kartoffelfighter/temperatureLogger/wifiSens/Schematic/file5A52C998.sch

## KiCad design wifiSens/Schematic/file5A52C998.sch (2018-06-29)

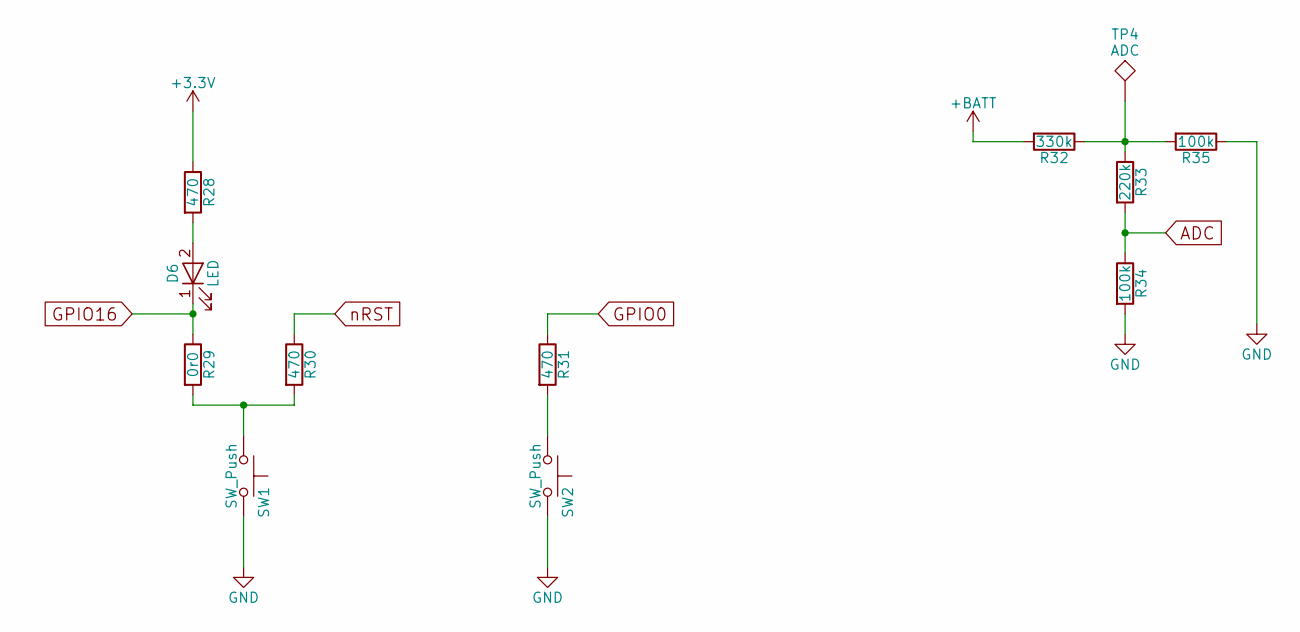
[picture p4: schematic file5A52C998.sch]

Parts:
D6: LED; LED_0805_HandSoldering
R28, R30, R31: 470; R_0603
R29: 0r0; R_0603
R32: 330k; R_0603
R33: 220k; R_0603
R34, R35: 100k; R_0603
SW1, SW2: SW_Push; SW_MEC_5GSH9
TP4: ADC; Pin_Header_Straight_1x01_Pitch1.00mm

Connections:
+3.3V: R28.1
+BATT: R32.2
ADC: R33.2, R34.1
GND: R34.2, R35.1, SW1.2, SW2.2
GPIO0: R31.1
GPIO16: D6.1 (K), R29.1
unnamed: D6.2 (A), R28.2
unnamed: R29.2, R30.2, SW1.1
unnamed: R31.2, SW2.1
unnamed: R32.1, R33.1, R35.2, TP4.1
nRST: R30.1
