kartoffelfighter/temperatureLogger/wifiSens/Schematic/file5A520BA4.sch

## KiCad design wifiSens/Schematic/file5A520BA4.sch (2018-06-29)

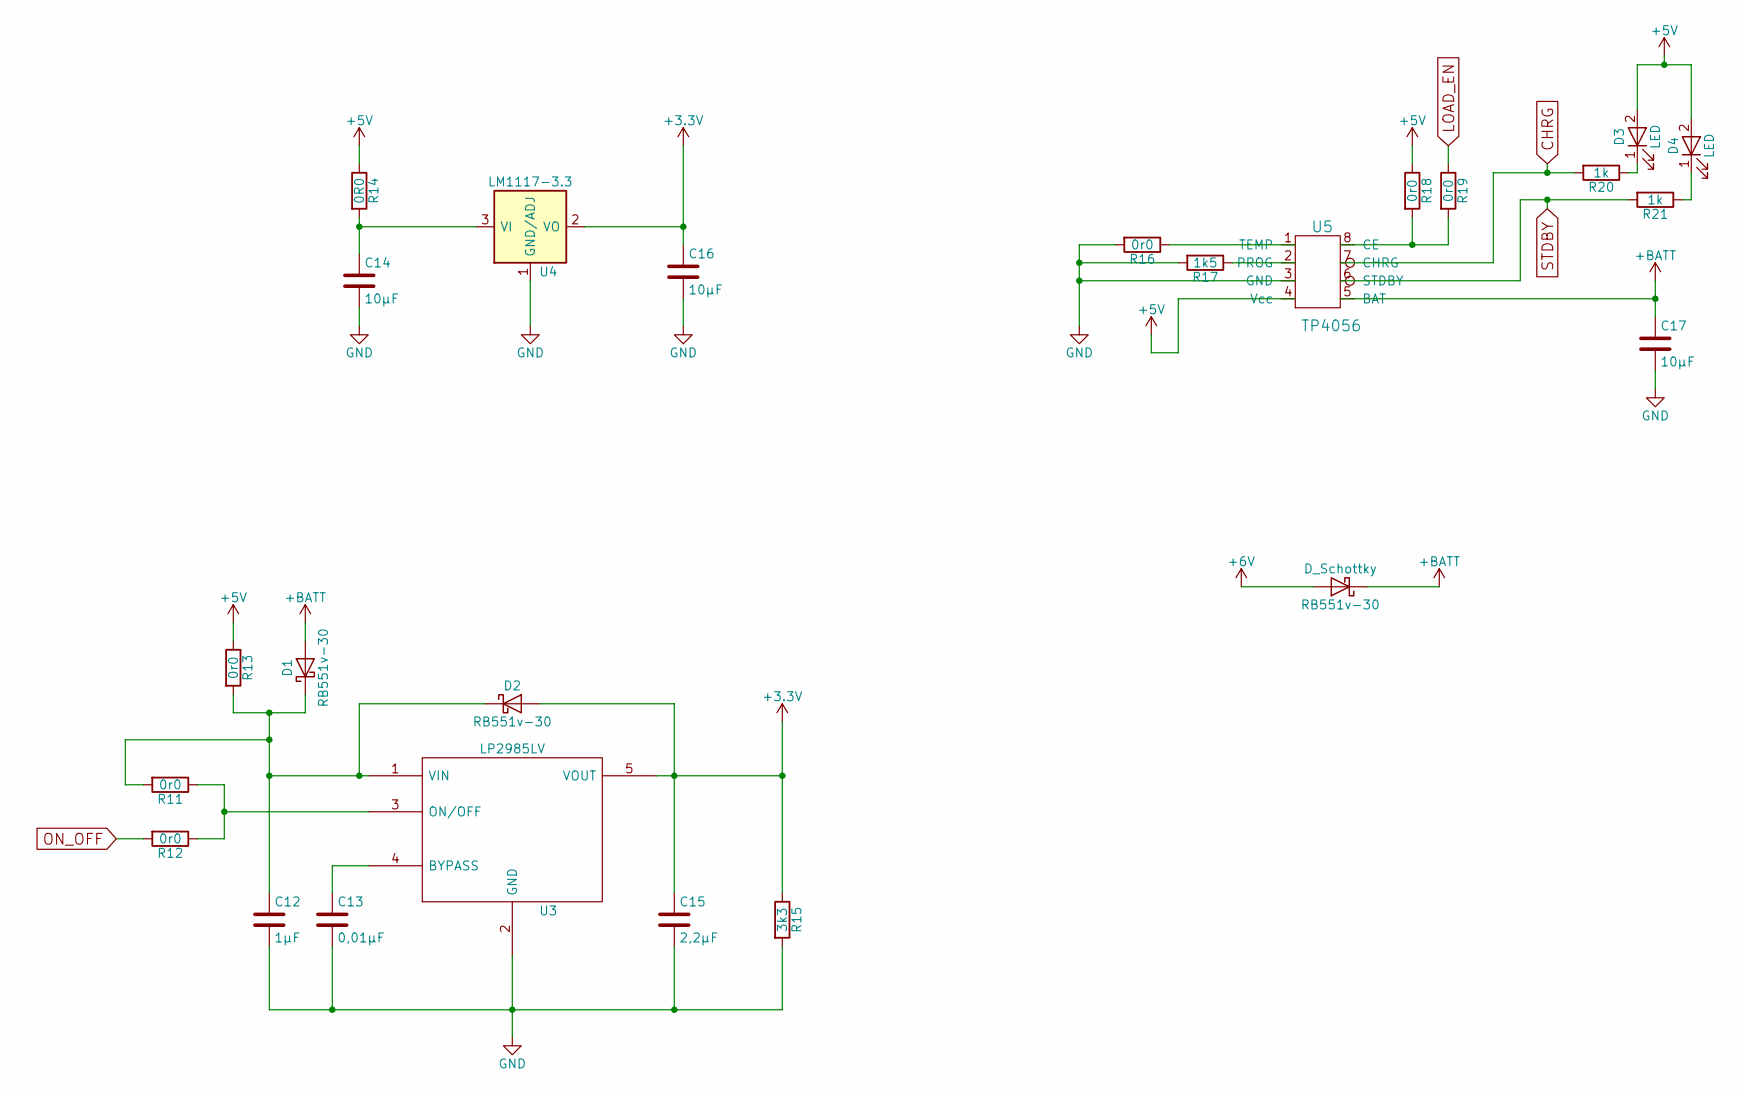
[picture p5: schematic file5A520BA4.sch]

Parts:
C12: 1µF; C_0603_HandSoldering
C13: 0,01µF; C_0603_HandSoldering
C14, C16, C17: 10µF; C_0603_HandSoldering
C15: 2,2µF; C_0603_HandSoldering
D1, D2: RB551v-30; D_SOD-323
D3, D4: LED; LED_0805_HandSoldering
R11, R12, R13, R16, R18, R19: 0r0; R_0603
R14: 0R0; R_0603
R15: 3k3; R_0603
R17: 1k5; R_0603
R20, R21: 1k; R_0603
RB551v-30: D_Schottky; D_SOD-323
U3: LP2985LV; SOT-23-5_HandSoldering
U4: LM1117-3.3; SOT-223
U5: TP4056; SuperSOT-8

Connections:
+3.3V: C15.1, C16.1, D2.2 (A), R15.1, U3.5 (VOUT), U4.2 (VO), U4.4 (VO)
+5V: D3.2 (A), D4.2 (A), R13.1, R14.1, R18.1, U5.4 (Vcc)
+6V: RB551v-30.2 (A)
+BATT: C17.1, D1.2 (A), RB551v-30.1 (K), U5.5 (BAT)
CHRG: R20.2, U5.7 (CHRG)
GND: C12.2, C13.2, C14.2, C15.2, C16.2, C17.2, R15.2, R16.2, R17.2, U3.2 (GND), U4.1 (GND/ADJ), U5.3 (GND)
LOAD_EN: R19.1
unnamed: C12.1, D1.1 (K), D2.1 (K), R11.2, R13.2, U3.1 (VIN)
unnamed: C13.1, U3.4 (BYPASS)
unnamed: C14.1, R14.2, U4.3 (VI)
unnamed: D3.1 (K), R20.1
unnamed: D4.1 (K), R21.1
unnamed: R11.1, R12.1, U3.3 (ON/OFF)
unnamed: R16.1, U5.1 (TEMP)
unnamed: R17.1, U5.2 (PROG)
unnamed: R18.2, R19.2, U5.8 (CE)
ON_OFF: R12.2
STDBY: R21.2, U5.6 (STDBY)
