kartoffelfighter/temperatureLogger/wifiSens/Schematic/file5A520BEC.sch

## KiCad design wifiSens/Schematic/file5A520BEC.sch (2018-06-29)

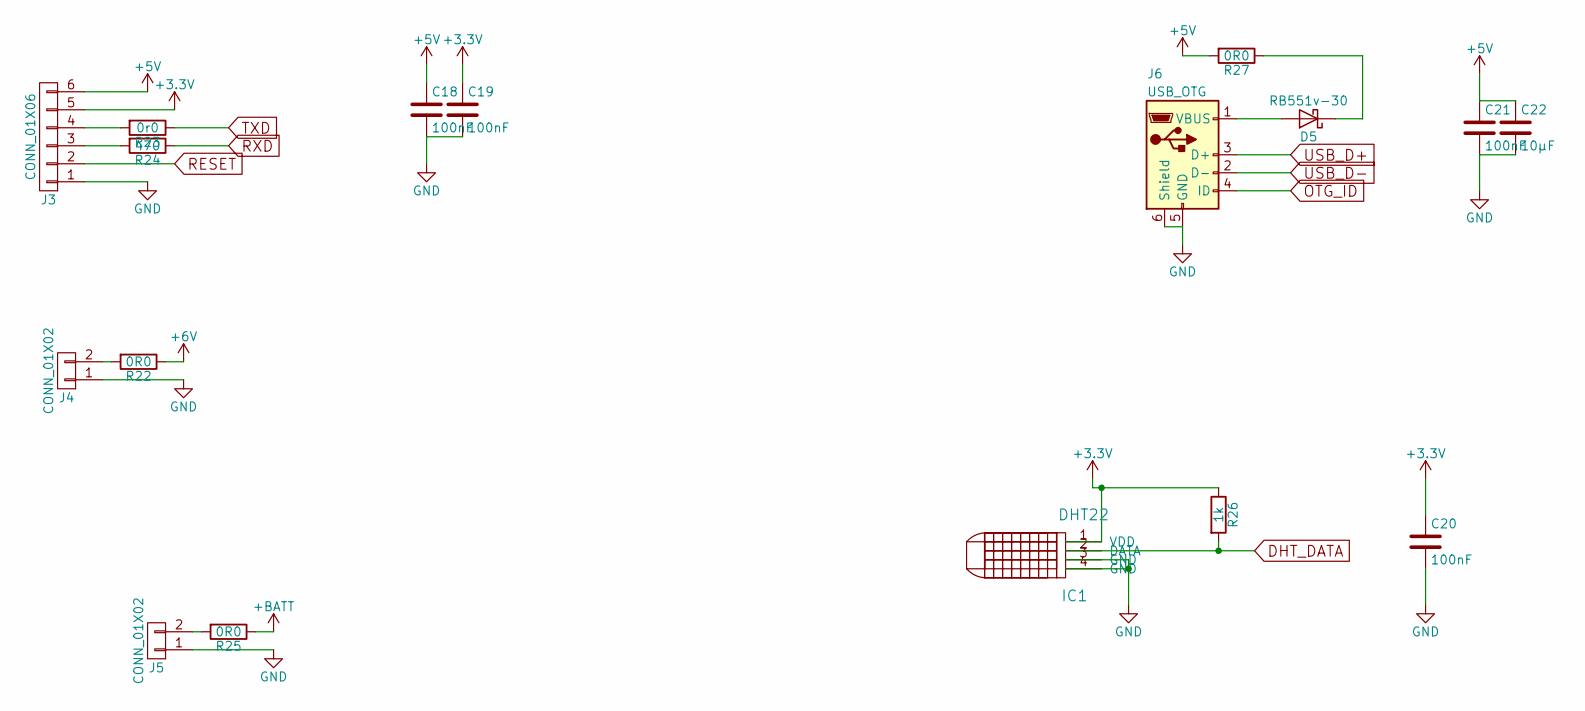
[picture p6: schematic file5A520BEC.sch]

Parts:
C18, C19, C20, C21: 100nF; C_0603_HandSoldering
C22: 10µF; C_1206_HandSoldering
D5: RB551v-30; D_SOD-323
IC1: DHT22; Pin_Header_Straight_1x04_Pitch2.54mm
J3: CONN_01X06; Pin_Header_Straight_1x06_Pitch2.54mm
J4, J5: CONN_01X02; Pin_Header_Straight_1x02_Pitch2.54mm
J6: USB_OTG; USB_Micro-B
R22, R25, R27: 0R0; R_0603
R23: 0r0; R_0603
R24: 470; R_0603
R26: 1k; R_0603

Connections:
+3.3V: C19.1, C20.1, IC1.1 (VDD), J3.5, R26.1
+5V: C18.1, C21.1, C22.1, J3.6, R27.2
+6V: R22.1
+BATT: R25.1
DHT_DATA: IC1.2 (DATA), R26.2
GND: C18.2, C19.2, C20.2, C21.2, C22.2, IC1.3 (GND), IC1.4 (GND), J3.1, J4.1, J5.1, J6.5 (GND), J6.6 (Shield)
unnamed: D5.1 (K), R27.1
unnamed: D5.2 (A), J6.1 (VBUS)
unnamed: J3.3, R24.2
unnamed: J3.4, R23.2
unnamed: J4.2, R22.2
unnamed: J5.2, R25.2
OTG_ID: J6.4 (ID)
RESET: J3.2
RXD: R24.1
TXD: R23.1
USB_D+: J6.3 (D+)
USB_D-: J6.2 (D-)
