kartoffelfighter/temperatureLogger/wifiSens/Schematic/file5A51535C.sch

## KiCad design wifiSens/Schematic/file5A51535C.sch (2018-06-29)

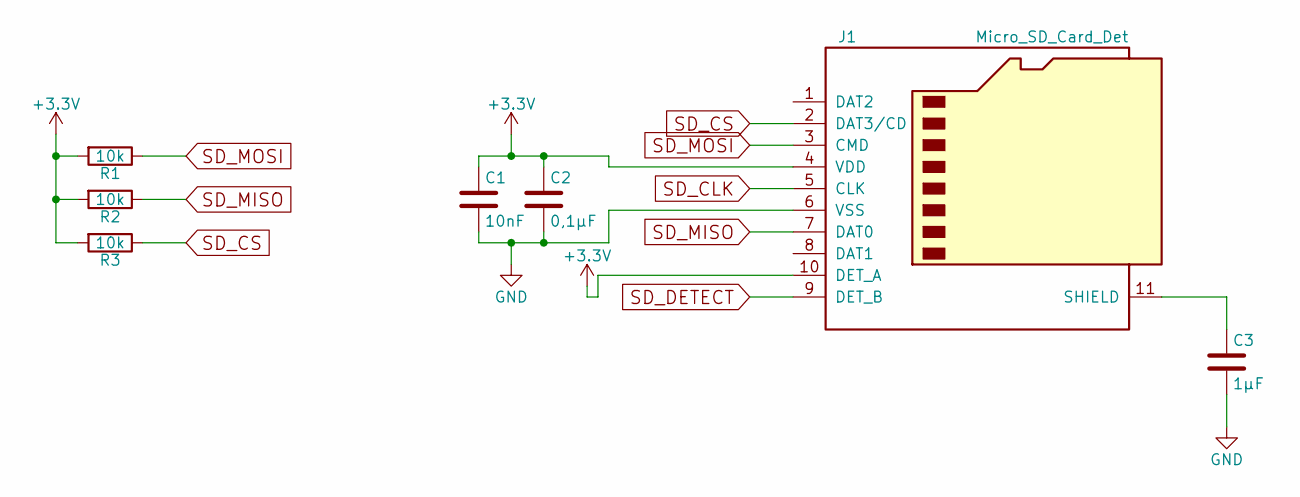
[picture p7: schematic file5A51535C.sch]

Parts:
C1: 10nF; C_0603_HandSoldering
C2: 0,1µF; C_0603_HandSoldering
C3: 1µF; C_0603_HandSoldering
J1: Micro_SD_Card_Det; Conn_uSDcard
R1, R2, R3: 10k; R_0603

Connections:
+3.3V: C1.1, C2.1, J1.4 (VDD), J1.10 (DET_A), R1.2, R2.2, R3.2
GND: C1.2, C2.2, C3.2, J1.6 (VSS)
unnamed: C3.1, J1.11 (SHIELD)
SD_CLK: J1.5 (CLK)
SD_CS: J1.2 (DAT3/CD), R3.1
SD_DETECT: J1.9 (DET_B)
SD_MISO: J1.7 (DAT0), R2.1
SD_MOSI: J1.3 (CMD), R1.1
