kartoffelfighter/temperatureLogger/wifiSens/Schematic/file5A51537C.sch

## KiCad design wifiSens/Schematic/file5A51537C.sch (2018-06-29)

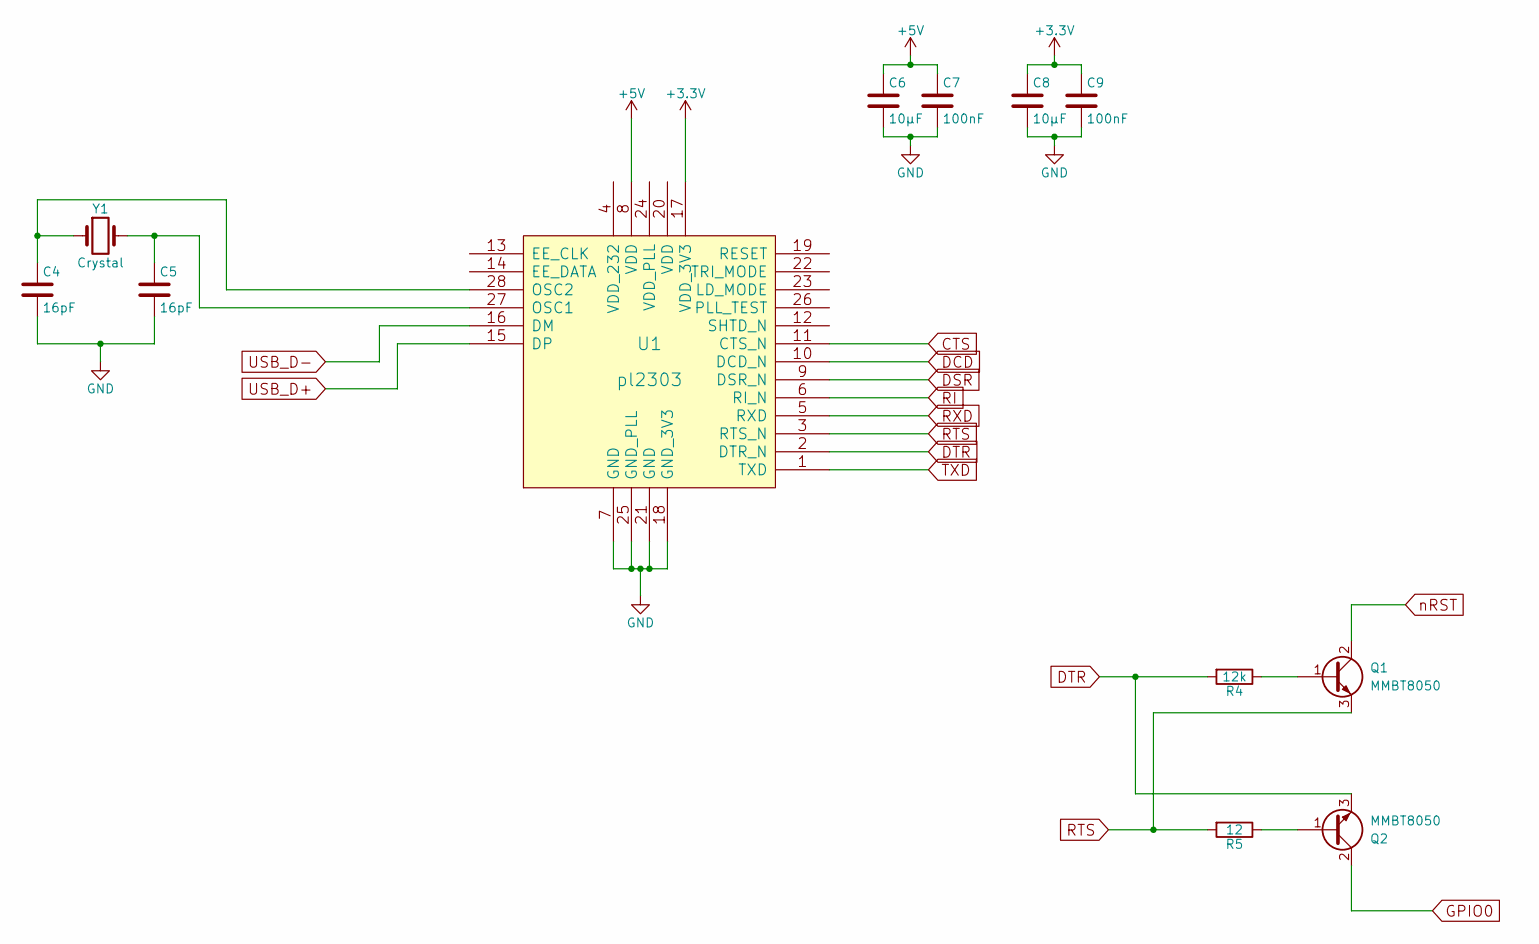
[picture p8: schematic file5A51537C.sch]

Parts:
C4, C5: 16pF; C_0603_HandSoldering
C6, C8: 10µF; C_0603_HandSoldering
C7, C9: 100nF; C_0603_HandSoldering
Q1, Q2: MMBT8050; SOT-23
R4: 12k; R_0603
R5: 12; R_0603
U1: pl2303; SSOP-28_5.3x10.2mm_Pitch0.65mm
Y1: Crystal; Crystal_SMD_HC49-SD_HandSoldering

Connections:
+3.3V: C8.1, C9.1, U1.17 (VDD_3V3)
+5V: C6.1, C7.1, U1.8 (VDD)
CTS: U1.11 (CTS_N)
DCD: U1.10 (DCD_N)
DSR: U1.9 (DSR_N)
DTR: Q2.3 (E), R4.2, U1.2 (DTR_N)
GND: C4.2, C5.2, C6.2, C7.2, C8.2, C9.2, U1.7 (GND), U1.18 (GND_3V3), U1.21 (GND), U1.25 (GND_PLL)
GPIO0: Q2.2 (C)
unnamed: C4.1, U1.28 (OSC2), Y1.1
unnamed: C5.1, U1.27 (OSC1), Y1.2
unnamed: Q1.1 (B), R4.1
unnamed: Q2.1 (B), R5.1
RI: U1.6 (RI_N)
RTS: Q1.3 (E), R5.2, U1.3 (RTS_N)
RXD: U1.5 (RXD)
TXD: U1.1 (TXD)
USB_D+: U1.15 (DP)
USB_D-: U1.16 (DM)
nRST: Q1.2 (C)
