kartoffelfighter/temperatureLogger/wifiSens/Schematic/file5A51538F.sch

## KiCad design wifiSens/Schematic/file5A51538F.sch (2018-06-29)

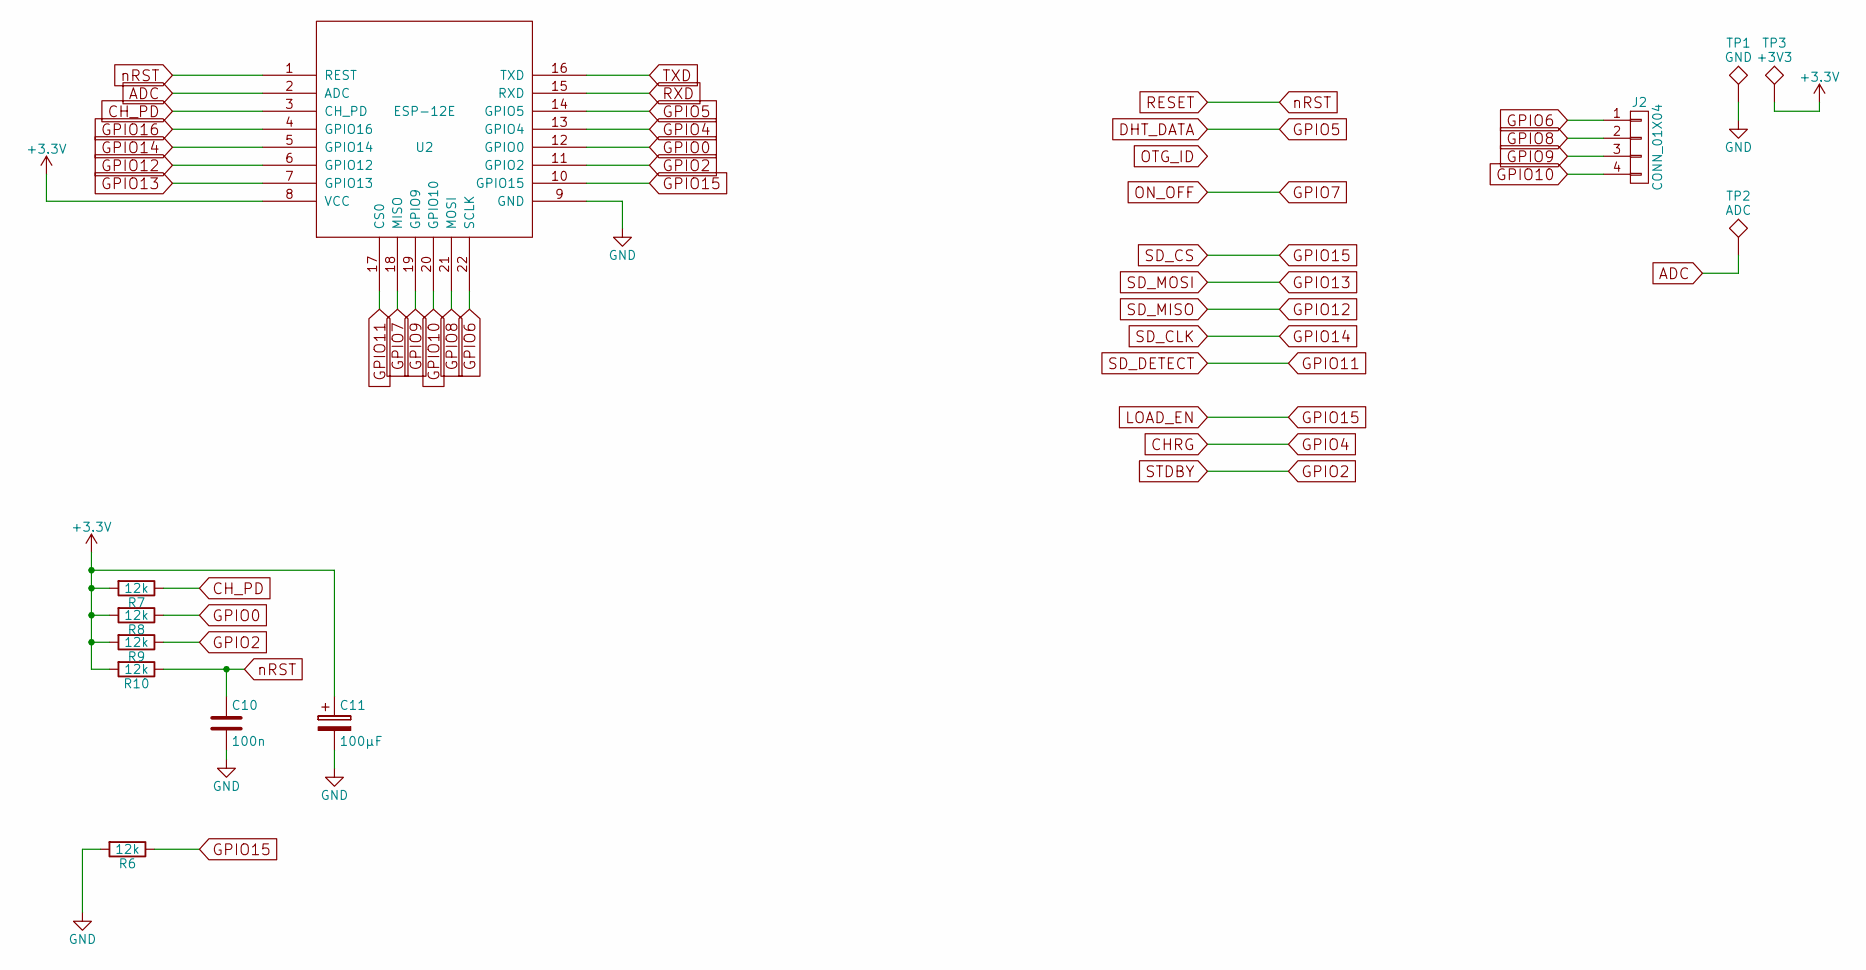
[picture p9: schematic file5A51538F.sch]

Parts:
C10: 100n; C_0603_HandSoldering
C11: 100µF; C_0603_HandSoldering
J2: CONN_01X04; Pin_Header_Straight_1x04_Pitch1.00mm
R6, R7, R8, R9, R10: 12k; R_0603
TP1: GND; Pin_Header_Straight_1x01_Pitch1.00mm
TP2: ADC; Pin_Header_Straight_1x01_Pitch1.00mm
TP3: +3V3; Pin_Header_Straight_1x01_Pitch1.00mm
U2: ESP-12E

Connections:
+3.3V: C11.1, R7.2, R8.2, R9.2, R10.2, TP3.1, U2.8 (VCC)
ADC: TP2.1, U2.2 (ADC)
CHRG: U2.13 (GPIO4)
CH_PD: R7.1, U2.3 (CH_PD)
DHT_DATA: U2.14 (GPIO5)
GND: C10.2, C11.2, R6.2, TP1.1, U2.9 (GND)
GPIO0: R8.1, U2.12 (GPIO0)
GPIO2: R9.1, U2.11 (GPIO2)
GPIO6: J2.1, U2.22 (SCLK)
GPIO7: U2.18 (MISO)
GPIO8: J2.2, U2.21 (MOSI)
GPIO9: J2.3, U2.19 (GPIO9)
GPIO10: J2.4, U2.20 (GPIO10)
GPIO11: U2.17 (CS0)
GPIO12: U2.6 (GPIO12)
GPIO13: U2.7 (GPIO13)
GPIO14: U2.5 (GPIO14)
GPIO15: R6.1, U2.10 (GPIO15)
GPIO16: U2.4 (GPIO16)
RXD: U2.15 (RXD)
TXD: U2.16 (TXD)
nRST: C10.1, R10.1, U2.1 (REST)
