kartoffelfighter/temperatureLogger/wifiSens/sourceCode/src/lang.h

// default Language

#define LCD_LANG de

#if (LCD_LANG == de)
  #define MSG_BOOT "Starte..."
  #define MSG_BOOT_1 "bitte warten"

  #define TEMP "Temperatur:"

  #define HUMID "Feuchtigkeit:"

  #define WIFI "Verbunden mit:"
  #define IP "IP-Adresse"

  #define TIME "Aktuelle Zeit"
#endif
